sissoux/LipOpenSink_passive/config_tool/config_gui.py

# Licensed under CERN-OHL-S-2.0
# © 2025 ADSTech [e-ddy]
# https://ohwr.org/licences/

"""
config_gui.py — E-DDY configuration GUI (Tkinter + pyserial)

Features
--------
- Auto-connect: scans serial ports, probes with "VER?" and opens the matching device.
- Robust command layer with timeouts and telemetry noise filtering.
- Live telemetry panel (VIN, TEMPADC, Temperature, FanIdx, Duty, LOAD, PG, MODE).
- Parameter editor with type/units validation and inline tooltips (hover bubbles).
- LUT management (pull/push) kept minimal for clarity; extend as needed.
- Start/Stop logging handled by the host application (separate feature).

Requirements
------------
- Python 3.9+
- pyserial
- tkinter (ships with CPython on Windows/macOS; on Linux: `sudo apt install python3-tk`)

Usage
-----
    pip install pyserial
    python config_tool/config_gui.py

This GUI talks to firmware built from code.py/uart_cmd.py in this repo.

License: MIT
"""

from __future__ import annotations

import threading
import time
import queue
import re
import sys
from dataclasses import dataclass
from typing import List, Tuple, Optional, Dict

import csv
import serial  # type: ignore
from serial.tools import list_ports  # type: ignore
import tkinter as tk
from tkinter import ttk, messagebox, filedialog

APP_NAME = "E-DDY Config"
EXPECTED_NAME = "E-DDY"
MIN_FW = (1, 3, 1)  # minimal compatible firmware version (major, minor, patch)

CSV_HEADER = [
    "vin_v",
    "tempadc_v",
    "temp_c",
    "fan_idx",
    "duty_pct",
    "load",
    "pg",
    "mode",
]

PARAM_SCHEMA = {
    # key: (label, tooltip, validator)
    "MIN_FAN_DUTY": (
        "Min fan duty",
        "Duty applied below first temperature threshold. Range: 0.0 – 1.0",
        lambda s: 0.0 <= float(s) <= 1.0,
    ),
    "HYST_C": (
        "Hysteresis (°C)",
        "Temperature hysteresis for fan steps and load re-enable. Typical: 5°C",
        lambda s: 0.0 <= float(s) <= 50.0,
    ),
    "LOAD_TRIP_C": (
        "Load cutoff (°C)",
        "Temperature to disable LOAD_EN. LOAD re-enables at (cutoff - hysteresis)",
        lambda s: 20.0 <= float(s) <= 130.0,
    ),
    "FAST_DT_MS": (
        "Fast loop (ms)",
        "Control/ADC loop period in milliseconds. Typical: 5",
        lambda s: 1 <= int(float(s)) <= 100,
    ),
    "FC_TEMP_HZ": (
        "Temp LPF (Hz)",
        "IIR cutoff for temperature channel. Lower = more smoothing",
        lambda s: 0.0 <= float(s) <= 5.0,
    ),
    "FC_VIN_HZ": (
        "Vin LPF (Hz)",
        "IIR cutoff for VIN channel. Lower = more smoothing",
        lambda s: 0.0 <= float(s) <= 5.0,
    ),
    "RAMP_TIME_MS": (
        "Ramp time (ms)",
        "Time to move from current to new duty target",
        lambda s: 0 <= int(float(s)) <= 60000,
    ),
    "RAMP_STEP_MS": (
        "Ramp update (ms)",
        "Duty update interval during ramp",
        lambda s: 1 <= int(float(s)) <= 5000,
    ),
    "TELEM_RATE_MS": (
        "Telemetry (ms)",
        "Period of device telemetry. 0 disables. GUI sets this automatically",
        lambda s: 0 <= int(float(s)) <= 10000,
    ),
    "TELEM_FORMAT": (
        "Telemetry format",
        "CSV or HUMAN. GUI uses CSV for easier parsing",
        lambda s: s.strip().upper() in ("CSV", "HUMAN"),
    ),
    "TEMP_CAL_A": (
        "Temp cal. A",
        "Calibration coefficient A for temperature voltage: y=A*x+B",
        lambda s: -10.0 <= float(s) <= 10.0,
    ),
    "TEMP_CAL_B": (
        "Temp cal. B",
        "Calibration offset B for temperature voltage (Volts)",
        lambda s: -100.0 <= float(s) <= 100.0,
    ),
    "VIN_CAL_A": (
        "Vin cal. A",
        "Calibration coefficient A for VIN: y=A*x+B",
        lambda s: -10.0 <= float(s) <= 25.0,
    ),
    "VIN_CAL_B": (
        "Vin cal. B",
        "Calibration offset B for VIN (Volts)",
        lambda s: -5.0 <= float(s) <= 5.0,
    ),
    "LOAD_TRIP_V": (
        "Load cutoff (V)",
        "Voltage to disable LOAD_EN. LOAD re-enables at (cutoff - hysteresis)",
        lambda s: 5.0 <= float(s) <= 15.0,
    ),
    "HYST_V": (
        "Hysteresis (V)",
        "Voltage hysteresis for load re-enable. Typical: 0.5V",
        lambda s: 0.0 <= float(s) <= 5.0,
    ),
    "BYPASS_VIN_CUTOFF": (
        "Bypass VIN cutoff",
        "1 = Disable VIN undervoltage cutoff (bypass). 0 = Enforce cutoff",
        lambda s: int(float(s)) in (0, 1),
    ),
}

PARAM_ORDER = [
    "MIN_FAN_DUTY",
    "HYST_C",
    "LOAD_TRIP_C",
    "FAST_DT_MS",
    "FC_TEMP_HZ",
    "FC_VIN_HZ",
    "RAMP_TIME_MS",
    "RAMP_STEP_MS",
    "TELEM_RATE_MS",
    "TELEM_FORMAT",
    "TEMP_CAL_A",
    "TEMP_CAL_B",
    "VIN_CAL_A",
    "VIN_CAL_B",
    "LOAD_TRIP_V",
    "HYST_V",
    "BYPASS_VIN_CUTOFF",
]


# ------------------------------
# Utilities
# ------------------------------

def parse_version(vs: str) -> Tuple[int, int, int]:
    """Parse version string like '1.3.0' into a tuple.

    Args:
        vs: Version string.
    Returns:
        (major, minor, patch)
    """
    m = re.match(r"(\d+)\.(\d+)\.(\d+)", vs.strip())
    if not m:
        return (0, 0, 0)
    return tuple(int(x) for x in m.groups())  # type: ignore


# ------------------------------
# Serial device wrapper
# ------------------------------

class Dev:
    """Serial device wrapper for the firmware protocol.

    One background thread reads the serial port and *classifies lines*:
      - Telemetry (CSV or HUMAN) → telem_queue
      - Command responses (OK/ERR/VER/… and payload) → cmd_queue

    This prevents races between live telemetry and command requests.
    """

    def __init__(self, port: str, baud: int = 115200, timeout: float = 1.0):
        self.port = port
        self.baud = baud
        self.timeout = timeout
        self.ser: Optional[serial.Serial] = None
        # Two queues so telemetry doesn't steal command responses
        self.cmd_queue: "queue.Queue[str]" = queue.Queue()
        self.telem_queue: "queue.Queue[str]" = queue.Queue()
        self.rx_thread: Optional[threading.Thread] = None
        self.rx_stop = threading.Event()

    # --- lifecycle ---
    def open(self) -> None:
        """Open serial port and start RX thread."""
        self.ser = serial.Serial(self.port, self.baud, timeout=self.timeout, write_timeout=1.0)
        self.rx_stop.clear()
        self.rx_thread = threading.Thread(target=self._rx_loop, daemon=True)
        self.rx_thread.start()

    def close(self) -> None:
        """Stop RX thread and close serial port."""
        self.rx_stop.set()
        if self.rx_thread:
            self.rx_thread.join(timeout=1.0)
        if self.ser and self.ser.is_open:
            try:
                self.ser.close()
            except Exception:
                pass
        self.ser = None

    # --- low-level ---
    def write_line(self, line: str) -> None:
        """Write a line terminated with LF (device accepts CR/LF/CRLF)."""
        if not self.ser:
            raise RuntimeError("Port not open")
        data = (line.rstrip("\r\n") + "\n").encode("utf-8")
        self.ser.write(data)
        self.ser.flush()

    def _is_telem(self, s: str) -> bool:
        return ("," in s and s.count(",") >= 3) or s.startswith("VIN=")

    def _rx_loop(self) -> None:
        """Background read loop that classifies lines into cmd/telem queues."""
        assert self.ser is not None
        while not self.rx_stop.is_set():
            try:
                raw = self.ser.readline()
                if not raw:
                    continue
                s = raw.decode("utf-8", errors="replace").strip()
                if not s:
                    continue
                if self._is_telem(s):
                    self.telem_queue.put(s)
                else:
                    self.cmd_queue.put(s)
            except Exception:
                time.sleep(0.05)

    def cmd(self, line: str, expect_multiline: bool = False, deadline_s: float = 2.0) -> Tuple[str, List[str]]:
        """Send a command and wait for a response from the *cmd_queue*.

        Telemetry is handled separately and never consumes these responses.
        """
        if not self.ser:
            raise RuntimeError("Port not open")
        # drain old responses (but leave telemetry alone)
        while not self.cmd_queue.empty():
            try:
                self.cmd_queue.get_nowait()
            except Exception:
                break
        self.write_line(line)
        t0 = time.time()
        first = None
        payload: List[str] = []
        while time.time() - t0 < deadline_s:
            try:
                s = self.cmd_queue.get(timeout=0.1)
            except queue.Empty:
                continue
            if first is None:
                first = s
                if not expect_multiline:
                    return first, []
            else:
                payload.append(s)
                if s == "END":
                    break
        if first is None:
            raise RuntimeError("Timeout waiting for response")
        return first, payload

    # --- high-level helpers ---
    def telem_on(self, rate_ms: int = 250, fmt: str = "CSV") -> None:
        self.cmd(f"TELEM FORMAT {fmt}")
        self.cmd(f"TELEM RATE {rate_ms}")

    def telem_off(self) -> None:
        self.cmd("TELEM RATE 0")

    def get_params(self) -> Dict[str, str]:
        first, lines = self.cmd("GET PARAMS", expect_multiline=True, deadline_s=2.0)
        if not first.startswith("OK"):
            raise RuntimeError(first)
        out: Dict[str, str] = {}
        for s in lines:
            if s == "END":
                break
            if "=" in s:
                k, v = s.split("=", 1)
                out[k.strip()] = v.strip()
        return out

    def set_param(self, key: str, value: str) -> None:
        first, _ = self.cmd(f"SET {key} {value}")
        if not first.startswith("OK"):
            raise RuntimeError(first)

    def save(self) -> str:
        first, _ = self.cmd("SAVE", expect_multiline=False, deadline_s=3.0)
        if first.startswith("OK"):
            return first
        raise RuntimeError(first)

# ------------------------------
# Tk helpers: tooltip bubbles
# ------------------------------

class ToolTip:
    """Simple hover tooltip for Tk widgets."""

    def __init__(self, widget, text: str):
        self.widget = widget
        self.text = text
        self.tipwindow: Optional[tk.Toplevel] = None
        widget.bind("<Enter>", self.show)
        widget.bind("<Leave>", self.hide)

    def show(self, _event=None):
        if self.tipwindow or not self.text:
            return
        x = self.widget.winfo_rootx() + 20
        y = self.widget.winfo_rooty() + self.widget.winfo_height() + 5
        self.tipwindow = tw = tk.Toplevel(self.widget)
        tw.wm_overrideredirect(True)
        tw.wm_geometry(f"+{x}+{y}")
        label = tk.Label(
            tw,
            text=self.text,
            justify=tk.LEFT,
            relief=tk.SOLID,
            borderwidth=1,
            background="#ffffe0",
            padx=6,
            pady=4,
            font=("TkDefaultFont", 9),
            wraplength=320,
        )
        label.pack(ipadx=1)

    def hide(self, _event=None):
        if self.tipwindow:
            self.tipwindow.destroy()
            self.tipwindow = None


# ------------------------------
# Tk Application
# ------------------------------

class App(ttk.Frame):
    """Main Tk application for E-DDY configuration.

    - Auto-connect on startup (scans COM ports, asks VER?).
    - Live telemetry panel updated from a dedicated queue.
    - Parameter grid with validation and tooltips.
    - Calibration helpers for VIN and Temperature.
    """

    def __init__(self, master):
        super().__init__(master)
        self.master.title(APP_NAME)
        self.grid(sticky="nsew")
        for i in range(2):
            self.master.columnconfigure(i, weight=1)
        self.master.rowconfigure(0, weight=1)

        self.dev: Optional[Dev] = None
        self.fw_version_str: str = ""
        self.fw_version_tuple: Tuple[int, int, int] = (0, 0, 0)
        self.telemetry_running = False
        self.telemetry_thread: Optional[threading.Thread] = None
        self.telemetry_stop = threading.Event()
        # Track which params the device actually supports (from latest refresh)
        self.dev_param_keys: set[str] = set()

        # Recording state (temperature + fan duty @ 1 Hz)
        self.latest_telem: Dict[str, float] = {}
        self.rec_running: bool = False
        self.rec_interval_ms: int = 1000  # default 1 second
        self.rec_data: List[Tuple[float, float, float]] = []  # (time_s, temp_c, duty_pct)
        self.rec_t0: float = 0.0
        self._rec_after_id: Optional[str] = None

        # Top bar: port selection + connect controls
        self.port_var = tk.StringVar()
        self.baud_var = tk.StringVar(value="115200")

        bar = ttk.Frame(self)
        bar.grid(row=0, column=0, columnspan=2, sticky="ew", pady=6)
        bar.columnconfigure(3, weight=1)

        ttk.Label(bar, text="Port:").grid(row=0, column=0, padx=4)
        self.port_cb = ttk.Combobox(bar, textvariable=self.port_var, width=20, values=self._list_ports())
        self.port_cb.grid(row=0, column=1, padx=4)
        ttk.Button(bar, text="Refresh", command=self._refresh_ports).grid(row=0, column=2, padx=4)
        ttk.Label(bar, text="Baud:").grid(row=0, column=3, padx=4, sticky="e")
        ttk.Entry(bar, textvariable=self.baud_var, width=8).grid(row=0, column=4, padx=4)
        ttk.Button(bar, text="Auto-Connect", command=self.on_autoconnect).grid(row=0, column=5, padx=6)
        ttk.Button(bar, text="Connect", command=self.on_connect).grid(row=0, column=6, padx=6)
        ttk.Button(bar, text="Disconnect", command=self.on_disconnect).grid(row=0, column=7, padx=6)

        # Live Telemetry Panel
        telem = ttk.LabelFrame(self, text="Live Telemetry")
        telem.grid(row=1, column=0, sticky="nsew", padx=8, pady=6)
        self.telemlabels: Dict[str, tk.StringVar] = {}
        fields = [
            ("VIN (V)", "vin_v"),
            ("TEMPADC (V)", "tempadc_v"),
            ("TEMP (°C)", "temp_c"),
            ("FanIdx", "fan_idx"),
            ("Duty (%)", "duty_pct"),
            ("LOAD", "load"),
            ("PG", "pg"),
            ("Mode", "mode"),
        ]
        for r, (label, key) in enumerate(fields):
            ttk.Label(telem, text=label+":").grid(row=r, column=0, sticky="w", padx=6, pady=2)
            var = tk.StringVar(value="-")
            ttk.Label(telem, textvariable=var).grid(row=r, column=1, sticky="w", padx=6, pady=2)
            self.telemlabels[key] = var

        # Parameters Panel
        params_frame = ttk.LabelFrame(self, text="Parameters")
        params_frame.grid(row=1, column=1, sticky="nsew", padx=8, pady=6)
        # Store per-parameter Tk variables and widgets
        # Note: vars may be StringVar or IntVar depending on control type
        self.param_vars: Dict[str, tk.Variable] = {}
        self.param_entries: Dict[str, tk.Widget] = {}
        for i, key in enumerate(PARAM_ORDER):
            label, tip, _validator = PARAM_SCHEMA[key]
            ttk.Label(params_frame, text=label+":").grid(row=i, column=0, sticky="e", padx=6, pady=2)
            # Control types per-parameter
            if key == "BYPASS_VIN_CUTOFF":
                # Checkbox (1 = bypass enabled, 0 = enforce cutoff)
                var = tk.IntVar(value=1)
                chk = ttk.Checkbutton(params_frame, variable=var)
                chk.grid(row=i, column=1, sticky="w", padx=6, pady=2)
                ToolTip(chk, f"{label}: {tip}\nKey: {key}\nChecked = 1 (bypass enabled), Unchecked = 0 (enforce cutoff)")
                self.param_vars[key] = var
                self.param_entries[key] = chk
            else:
                var = tk.StringVar(value="")
                # For MIN_FAN_DUTY, show entry in percent
                if key == "MIN_FAN_DUTY":
                    ent = ttk.Entry(params_frame, textvariable=var, width=14)
                    ent.grid(row=i, column=1, sticky="w", padx=6, pady=2)
                    ToolTip(ent, f"{label}: {tip}\nKey: {key}\nEnter as percent (0–100)")
                else:
                    ent = ttk.Entry(params_frame, textvariable=var, width=14)
                    ent.grid(row=i, column=1, sticky="w", padx=6, pady=2)
                    ToolTip(ent, f"{label}: {tip}\nKey: {key}")
                self.param_vars[key] = var
                self.param_entries[key] = ent

        # Bottom bar: actions
        actions = ttk.Frame(self)
        actions.grid(row=2, column=0, columnspan=2, sticky="ew", padx=8, pady=8)
        ttk.Button(actions, text="Refresh Params", command=self.on_refresh).grid(row=0, column=0, padx=4)
        ttk.Button(actions, text="Apply Params", command=self.on_apply).grid(row=0, column=1, padx=4)
        ttk.Button(actions, text="Save to Flash", command=self.on_save).grid(row=0, column=2, padx=4)
        ttk.Button(actions, text="Fan Auto", command=lambda: self._send('FAN AUTO')).grid(row=0, column=3, padx=4)
        # Manual Fan Duty Entry (percent)
        # ttk.Label(actions, text="Fan Duty (%):").grid(row=0, column=4, padx=4)
        ttk.Button(actions, text="Set Fan Duty", command=self.on_set_fan_duty).grid(row=0, column=5, padx=4)
        self.fan_duty_var = tk.StringVar(value="40")
        ttk.Entry(actions, textvariable=self.fan_duty_var, width=6).grid(row=0, column=6, padx=2)
        # ttk.Button(actions, text="Quiet", command=lambda: self._send('QUIET')).grid(row=0, column=7, padx=4)
        # Calibration buttons
        ttk.Button(actions, text="Cal VIN (1pt)", command=self.on_cal_vin_1pt).grid(row=0, column=7, padx=8)
        ttk.Button(actions, text="Cal VIN (2pt)", command=self.on_cal_vin_2pt).grid(row=0, column=8, padx=4)
        ttk.Button(actions, text="Cal TEMP (1pt)", command=self.on_cal_temp_1pt).grid(row=0, column=9, padx=8)

        # Recording controls
        self.btn_start_rec = ttk.Button(actions, text="Start Rec", command=self.on_start_rec)
        self.btn_start_rec.grid(row=0, column=10, padx=8)
        self.btn_stop_rec = ttk.Button(actions, text="Stop", command=self.on_stop_rec, state="disabled")
        self.btn_stop_rec.grid(row=0, column=11, padx=4)

        # Status bar
        self.status = tk.StringVar(value="Disconnected")
        ttk.Label(self, textvariable=self.status, anchor="w").grid(row=3, column=0, columnspan=2, sticky="ew", padx=8, pady=(0,8))

        # Expand behavior
        self.columnconfigure(0, weight=1)
        self.columnconfigure(1, weight=1)
        self.rowconfigure(1, weight=1)

    # ---- port management ----
    def _list_ports(self) -> List[str]:
        return [p.device for p in list_ports.comports()]

    def _refresh_ports(self) -> None:
        self.port_cb["values"] = self._list_ports()

    # ---- connect / disconnect ----
    def on_connect(self) -> None:
        port = self.port_var.get().strip()
        if not port:
            messagebox.showwarning(APP_NAME, "Choose a serial port or use Auto-Connect")
            return
        try:
            self._open_dev(port)
            self.status.set(f"Connected on {port}")
        except Exception as e:
            messagebox.showerror("Connect", str(e))
            self.status.set("Disconnected")

    def on_autoconnect(self) -> None:
        """Scan COM ports, probe with VER?, connect when compatible."""
        ports = self._list_ports()
        if not ports:
            messagebox.showinfo(APP_NAME, "No serial ports found.")
            return
        incompatible: list[tuple[str,str]] = []  # (port, version)
        detected_any = False
        for port in ports:
            try:
                tmp = Dev(port, int(self.baud_var.get()))
                tmp.open()
                # small settle
                time.sleep(0.2)
                # QUIET (in case telemetry is noisy)
                try:
                    tmp.cmd("QUIET", deadline_s=0.8)
                except Exception:
                    pass
                # Ask version
                first, _ = tmp.cmd("VER?", deadline_s=1.2)
                if first.startswith("VER "):
                    ver = first.split(" ", 1)[1].strip()
                    vtuple = parse_version(ver)
                    detected_any = True
                    if vtuple >= MIN_FW:
                        # Found compatible device
                        tmp.close()
                        self.port_var.set(port)
                        self._open_dev(port)
                        self.status.set(f"Auto-connected on {port} (FW {ver})")
                        return
                    else:
                        incompatible.append((port, ver))
                tmp.close()
            except Exception:
                try:
                    tmp.close()
                except Exception:
                    pass
                continue
        # Post-scan outcome handling
        if incompatible and not detected_any:
            # Should not happen: incompatible implies detected_any, but guard anyway
            messagebox.showwarning(APP_NAME, "No compatible device found.")
        elif incompatible:
            min_str = ".".join(str(x) for x in MIN_FW)
            details = "\n".join(f"- {p}: FW {v}" for (p,v) in incompatible)
            messagebox.showwarning(
                APP_NAME,
                "Firmware version incompatibility:\n"
                f"Required >= {min_str}. Found older versions on:\n{details}\n\n"
                "Please flash firmware {} or newer and retry.".format(min_str)
            )
        else:
            messagebox.showwarning(APP_NAME, "No compatible device found.")

    def _open_dev(self, port: str) -> None:
        if self.dev:
            try: self.dev.close()
            except Exception: pass
        self.dev = Dev(port, int(self.baud_var.get()))
        self.dev.open()
        # sanity: QUIET + PING
        try: self.dev.cmd("QUIET", deadline_s=0.8)
        except Exception: pass
        first, _ = self.dev.cmd("PING", deadline_s=0.8)
        if not (first.startswith("PONG") or first.startswith("OK")):
            raise RuntimeError(f"Unexpected PING response: {first}")
        # Version check
        try:
            ver_first, _ = self.dev.cmd("VER?", deadline_s=1.2)
            if ver_first.startswith("VER "):
                ver = ver_first.split(" ", 1)[1].strip()
                self.fw_version_str = ver
                self.fw_version_tuple = parse_version(ver)
                min_str = ".".join(str(x) for x in MIN_FW)
                if self.fw_version_tuple < MIN_FW:
                    messagebox.showwarning(
                        APP_NAME,
                        f"Firmware {ver} detected. This GUI expects >= {min_str}.\n"
                        "Some features will be disabled. Please update the device firmware.",
                    )
                # Show version in status bar
                self.status.set(f"Connected on {port} (FW {ver})")
        except Exception:
            # Non-fatal; continue without version details
            pass
        # Enable telemetry for live view
        self.dev.telem_on(rate_ms=250, fmt="CSV")
        self._start_telem_reader()
        self.on_refresh()

    def on_disconnect(self) -> None:
        self._stop_telem_reader()
        # Stop recording if active (without prompting to save)
        self._cancel_rec_timer() if hasattr(self, "_rec_after_id") else None
        self.rec_running = False
        if hasattr(self, "btn_start_rec"):
            self.btn_start_rec.state(["!disabled"])  # enable
        if hasattr(self, "btn_stop_rec"):
            self.btn_stop_rec.state(["disabled"])    # disable
        if self.dev:
            try:
                self.dev.telem_off()
                self.dev.close()
            except Exception:
                pass
        self.dev = None
        self.status.set("Disconnected")

    # ---- telemetry ----
    def _start_telem_reader(self) -> None:
        if self.telemetry_running:
            return
        self.telemetry_stop.clear()
        self.telemetry_thread = threading.Thread(target=self._telem_loop, daemon=True)
        self.telemetry_thread.start()
        self.telemetry_running = True

    def _stop_telem_reader(self) -> None:
        self.telemetry_stop.set()
        if self.telemetry_thread:
            self.telemetry_thread.join(timeout=1.0)
        self.telemetry_running = False

    def _telem_loop(self) -> None:
        assert self.dev is not None
        q = self.dev.telem_queue
        while not self.telemetry_stop.is_set():
            try:
                s = q.get(timeout=0.25)
            except queue.Empty:
                continue
            if not s:
                continue
            # Parse CSV telemetry only
            if "," in s and s.count(",") >= 3:
                parts = s.split(",")
                if len(parts) >= len(CSV_HEADER):
                    data = dict(zip(CSV_HEADER, parts))
                    self._update_telem_labels(data)

    def _update_telem_labels(self, data: Dict[str, str]) -> None:
        def setv(key, fmt=None):
            val = data.get(key, "-")
            if fmt:
                try:
                    val = fmt(float(val))
                except Exception:
                    pass
            self.telemlabels[key].set(str(val))
        # Numerical formatting
        setv("vin_v", lambda x: f"{x:.3f}")
        setv("tempadc_v", lambda x: f"{x:.3f}")
        setv("temp_c", lambda x: f"{x:.1f}")
        setv("fan_idx")
        setv("duty_pct", lambda x: f"{x:.0f}")
        setv("load")
        setv("pg")
        setv("mode")

        # Keep latest numeric telemetry for recording
        try:
            self.latest_telem["temp_c"] = float(data.get("temp_c", "nan"))
        except Exception:
            pass
        try:
            self.latest_telem["duty_pct"] = float(data.get("duty_pct", "nan"))
        except Exception:
            pass

    # ---- recording: temp + fan duty → CSV ----
    def _rec_tick(self) -> None:
        if not self.rec_running:
            return
        # Sample latest values
        t = time.time() - self.rec_t0
        temp = self.latest_telem.get("temp_c")
        duty = self.latest_telem.get("duty_pct")
        if temp is not None and duty is not None:
            try:
                self.rec_data.append((float(t), float(temp), float(duty)))
            except Exception:
                pass
        # schedule next
        self._rec_after_id = self.after(self.rec_interval_ms, self._rec_tick)

    def _cancel_rec_timer(self) -> None:
        if self._rec_after_id is not None:
            try:
                self.after_cancel(self._rec_after_id)
            except Exception:
                pass
            self._rec_after_id = None

    def on_start_rec(self) -> None:
        if not self.dev:
            messagebox.showwarning(APP_NAME, "Connect to a device first.")
            return
        if self.rec_running:
            return
        self.rec_data = []
        self.rec_t0 = time.time()
        self.rec_running = True
        self.btn_start_rec.state(["disabled"])  # disable
        self.btn_stop_rec.state(["!disabled"])  # enable
        self.status.set("Recording started (1 Hz)")
        self._rec_tick()

    def on_stop_rec(self) -> None:
        if not self.rec_running:
            return
        self.rec_running = False
        self._cancel_rec_timer()
        # Prompt for save location
        default_name = time.strftime("record_%Y%m%d_%H%M%S.csv")
        path = filedialog.asksaveasfilename(
            title="Save recording as…",
            defaultextension=".csv",
            filetypes=[("CSV files", "*.csv"), ("All files", "*.*")],
            initialfile=default_name,
        )
        if path:
            try:
                with open(path, "w", newline="", encoding="utf-8") as f:
                    writer = csv.writer(f)
                    writer.writerow(["time_s", "temp_c", "fan_duty_pct"])
                    writer.writerows(self.rec_data)
                self.status.set(f"Saved {len(self.rec_data)} samples → {path}")
            except Exception as e:
                messagebox.showerror("Save CSV", str(e))
        else:
            # User canceled save dialog; keep data for this session
            self.status.set("Recording stopped (save canceled)")
        # Reset buttons
        self.btn_start_rec.state(["!disabled"])  # enable
        self.btn_stop_rec.state(["disabled"])    # disable

    # ---- Calibration Helpers ----
    def _get_params_dict(self) -> Dict[str, float]:
        p = self.dev.get_params()
        out: Dict[str, float] = {}
        for k, v in p.items():
            try:
                out[k] = float(v) if k != "TELEM_FORMAT" else v
            except Exception:
                pass
        return out

    def _raw_volts(self) -> Tuple[float, float]:
        # Requires firmware support: RAW? → OK + one payload line: "vin_raw_v,tempadc_raw_v"
        first, lines = self.dev.cmd("RAW?", expect_multiline=True, deadline_s=1.0)
        if not first.startswith("OK"):
            raise RuntimeError(first)
        line = lines[0] if lines else ""
        parts = line.split(",")
        if len(parts) < 2:
            raise RuntimeError("RAW? bad payload")
        return float(parts[0]), float(parts[1])

    def _tempv_for(self, t_c: float) -> float:
        # Requires firmware support: TEMPV? <T> → OK + one payload line with volts
        first, lines = self.dev.cmd(f"TEMPV? {t_c}", expect_multiline=True, deadline_s=1.0)
        if not first.startswith("OK"):
            raise RuntimeError(first)
        line = lines[0] if lines else ""
        return float(line.strip())
    
    def on_cal_vin_1pt(self) -> None:
        """Calibrate VIN slope (A) by averaging readings for 5 seconds and comparing to actual VIN. Offset (B) is assumed zero."""
        if not self.dev:
            return
        try:
            s = tk.simpledialog.askstring(APP_NAME, "5 seconds single point calibration. Enter actual VIN (Volts):")
            if not s:
                return
            v_true = float(s)
            # Set calibration A and B to 1.0 and 0.0 first
            self.dev.set_param("VIN_CAL_A", "1.0")
            self.dev.set_param("VIN_CAL_B", "0.0")
            self.on_refresh()
            # Gather VIN readings for 5 seconds
            readings = []
            start = time.time()
            while time.time() - start < 5.0:
                try:
                    telem = self.dev.telem_queue.get(timeout=0.5)
                    parts = telem.split(",")
                    if len(parts) >= 1:
                        vin_read = float(parts[0])
                        readings.append(vin_read)
                except Exception:
                    pass
            if not readings:
                raise RuntimeError("No VIN readings received.")
            v_avg = sum(readings) / len(readings)
            # Calculate slope (A) assuming offset B=0
            if abs(v_avg) < 1e-6:
                raise RuntimeError("Averaged VIN reading too close to zero; cannot calibrate slope.")
            a_new = v_true / v_avg
            self.dev.set_param("VIN_CAL_A", str(a_new))
            self.on_refresh()
            messagebox.showinfo("Cal VIN (1pt)", f"VIN_CAL_A set to {a_new:.6f}\nAveraged reading: {v_avg:.6f} V\nOffset (B) assumed 0.0 V")
        except Exception as e:
            messagebox.showerror("Cal VIN (1pt)", str(e))

    def on_cal_vin_2pt(self) -> None:
        """Calibrate VIN slope (A) and offset (B) using two points and averaged readings."""
        if not self.dev:
            return
        try:
            # First point
            s1 = tk.simpledialog.askstring(APP_NAME, "Enter actual VIN #1 (Volts), then click OK:")
            if not s1:
                return
            v1 = float(s1)
            messagebox.showinfo("Cal VIN (2pt)", "Averaging readings for 5 seconds at VIN #1...")
            readings1 = []
            start = time.time()
            while time.time() - start < 5.0:
                try:
                    telem = self.dev.telem_queue.get(timeout=0.5)
                    parts = telem.split(",")
                    if len(parts) >= 1:
                        vin_read = float(parts[0])
                        readings1.append(vin_read)
                except Exception:
                    pass
            if not readings1:
                raise RuntimeError("No VIN readings received for point 1.")
            vin_raw1 = sum(readings1) / len(readings1)

            # Second point
            messagebox.showinfo("Cal VIN (2pt)", "Now change to the second known VIN and press OK")
            s2 = tk.simpledialog.askstring(APP_NAME, "Enter actual VIN #2 (Volts), then click OK:")
            if not s2:
                return
            v2 = float(s2)
            messagebox.showinfo("Cal VIN (2pt)", "Averaging readings for 5 seconds at VIN #2...")
            readings2 = []
            start = time.time()
            while time.time() - start < 5.0:
                try:
                    telem = self.dev.telem_queue.get(timeout=0.5)
                    parts = telem.split(",")
                    if len(parts) >= 1:
                        vin_read = float(parts[0])
                        readings2.append(vin_read)
                except Exception:
                    pass
            if not readings2:
                raise RuntimeError("No VIN readings received for point 2.")
            vin_raw2 = sum(readings2) / len(readings2)

            if abs(vin_raw2 - vin_raw1) < 1e-6:
                raise RuntimeError("Raw readings too close; choose distinct points.")

            # Calculate slope (A) and offset (B)
            a_new = (v2 - v1) / (vin_raw2 - vin_raw1)
            b_new = v1 - a_new * vin_raw1
            self.dev.set_param("VIN_CAL_A", str(a_new))
            self.dev.set_param("VIN_CAL_B", str(b_new))
            self.on_refresh()
            messagebox.showinfo("Cal VIN (2pt)", f"VIN_CAL_A={a_new:.6f}\nVIN_CAL_B={b_new:.6f}")
        except Exception as e:
            messagebox.showerror("Cal VIN (2pt)", str(e))

    def on_cal_temp_1pt(self) -> None:
        """Calibrate temperature offset by averaging readings for 5 seconds and comparing to actual temperature."""
        if not self.dev:
            return
        try:
            s = tk.simpledialog.askstring(APP_NAME, "5 seconds single point calibration. Enter actual Temperature (°C):")
            if not s:
                return
            t_true = float(s)
            # Gather temperature readings for 5 seconds
            readings = []
            start = time.time()
            while time.time() - start < 5.0:
                # Try to get a telemetry reading from the queue
                try:
                    telem = self.dev.telem_queue.get(timeout=0.5)
                    parts = telem.split(",")
                    if len(parts) >= 3:
                        t_read = float(parts[2])
                        readings.append(t_read)
                except Exception:
                    pass
            if not readings:
                raise RuntimeError("No temperature readings received.")
            t_avg = sum(readings) / len(readings)
            # B is the offset between real temperature and the readings
            b_new = t_true - t_avg + float(self._get_params_dict().get("TEMP_CAL_B", 0.0))
            self.dev.set_param("TEMP_CAL_B", str(b_new))
            self.on_refresh()
            messagebox.showinfo("Cal TEMP (1pt)", f"TEMP_CAL_B set to {b_new:.3f} °C\nAveraged reading: {t_avg:.3f} °C")
        except Exception as e:
            messagebox.showerror("Cal TEMP (1pt)", str(e))

    # ---- parameter flows ----
    def on_refresh(self) -> None:
        if not self.dev:
            return
        try:
            p = self.dev.get_params()
            # Record device-supported params
            try:
                self.dev_param_keys = set(p.keys())
            except Exception:
                self.dev_param_keys = set()
            for k, var in self.param_vars.items():
                # For MIN_FAN_DUTY, show as percent
                if k == "MIN_FAN_DUTY":
                    try:
                        var.set(str(round(float(p.get(k, "0")) * 100)))
                    except Exception:
                        var.set("")
                elif k == "BYPASS_VIN_CUTOFF":
                    # Map firmware numeric ("1"/"0" or floats) to checkbox state, default to 1 (bypass enabled)
                    try:
                        raw = p.get(k, "1")
                        iv = int(float(raw))
                        var.set(1 if iv != 0 else 0)
                    except Exception:
                        var.set(1)
                else:
                    var.set(str(p.get(k, "")))
            # Update widget enabled/disabled states robustly
            missing = []
            for k, w in self.param_entries.items():
                if k in self.dev_param_keys:
                    try:
                        w.configure(state="normal")
                    except Exception:
                        try: w.state(["!disabled"])  # fallback
                        except Exception: pass
                else:
                    missing.append(k)
                    try:
                        w.configure(state="disabled")
                    except Exception:
                        try: w.state(["disabled"])  # fallback
                        except Exception: pass
            if missing:
                self.status.set("Parameters loaded (unsupported: " + ", ".join(missing) + ")")
                # If firmware reports version >= MIN_FW but a critical param is missing, warn once.
                critical = ["BYPASS_VIN_CUTOFF"]
                if self.fw_version_tuple >= MIN_FW:
                    absent_critical = [c for c in critical if c in missing]
                    if absent_critical and not hasattr(self, "_warned_critical"):
                        self._warned_critical = True
                        messagebox.showwarning(
                            APP_NAME,
                            "Firmware reports version {} but missing parameter(s): {}.\n"
                            "You may be running an older build with the same version string. Flash the updated firmware to use these features.".format(
                                self.fw_version_str or "?",
                                ", ".join(absent_critical),
                            ),
                        )
            else:
                self.status.set("Parameters loaded")
        except Exception as e:
            messagebox.showerror("Refresh", str(e))

    def on_apply(self) -> None:
        if not self.dev:
            return
        try:
            # validate
            for k, var in self.param_vars.items():
                # Skip keys not supported by current firmware
                if self.dev_param_keys and (k not in self.dev_param_keys):
                    continue
                # Extract string value for validation based on control type
                if k == "BYPASS_VIN_CUTOFF":
                    val = str(int(var.get()))  # 0 or 1
                else:
                    # StringVar-backed entries
                    val = str(var.get()).strip()
                label, tip, validator = PARAM_SCHEMA[k]
                # For MIN_FAN_DUTY, validate percent
                if k == "MIN_FAN_DUTY":
                    try:
                        pct = float(val)
                        if not (0.0 <= pct <= 100.0):
                            raise ValueError
                        duty = pct / 100.0
                        if not validator(str(duty)):
                            raise ValueError
                    except Exception:
                        raise ValueError(f"Invalid value for {k}: {val}\nEnter percent (0–100)")
                elif k == "BYPASS_VIN_CUTOFF":
                    # Ensure 0/1
                    if val not in ("0", "1"):
                        raise ValueError(f"Invalid value for {k}: {val}\nExpected 0 or 1")
                else:
                    if not validator(val):
                        raise ValueError(f"Invalid value for {k}: {val}\n{tip}")
            # push
            skipped: list[str] = []
            for k, var in self.param_vars.items():
                # Skip keys not supported by current firmware
                if self.dev_param_keys and (k not in self.dev_param_keys):
                    skipped.append(k)
                    continue
                if k == "MIN_FAN_DUTY":
                    val = str(float(var.get()) / 100.0)
                    self.dev.set_param(k, val)
                elif k == "BYPASS_VIN_CUTOFF":
                    val = "1" if int(var.get()) != 0 else "0"
                    self.dev.set_param(k, val)
                else:
                    val = str(var.get()).strip()
                    self.dev.set_param(k, val)
            if skipped:
                self.status.set("Parameters applied (skipped: " + ", ".join(skipped) + ")")
            else:
                self.status.set("Parameters applied")
        except Exception as e:
            messagebox.showerror("Apply", str(e))

    def on_save(self) -> None:
        if not self.dev:
            return
        try:
            info = self.dev.save()
            messagebox.showinfo("Save", f"Saved: {info}")
        except Exception as e:
            messagebox.showerror("Save", str(e))

    # ---- misc ----
    def _send(self, line: str) -> None:
        if not self.dev:
            return
        try:
            self.dev.cmd(line)
        except Exception as e:
            messagebox.showerror("Command", str(e))

    def on_set_fan_duty(self) -> None:
        """Set manual fan duty from entry (percent)."""
        if not self.dev:
            return
        try:
            val = float(self.fan_duty_var.get())
            if not (0.0 <= val <= 100.0):
                raise ValueError("Duty must be between 0 and 100 percent")
            duty = val / 100.0
            self.dev.cmd(f"FAN DUTY {duty}")
            self.status.set(f"Fan duty set to {val:.0f}%")
        except Exception as e:
            messagebox.showerror("Fan Duty", str(e))


# ------------------------------
# main
# ------------------------------

def main() -> None:
    """Entry point."""
    root = tk.Tk()
    style = ttk.Style(root)
    if sys.platform.startswith("win"):
        style.theme_use("winnative")
    root.geometry("1080x620")
    app = App(root)
    root.protocol("WM_DELETE_WINDOW", lambda: (app.on_disconnect(), root.destroy()))
    root.mainloop()


if __name__ == "__main__":
    main()
